Pillazo/VRCHaptics/VRChat Udon/Every100ms.PNG

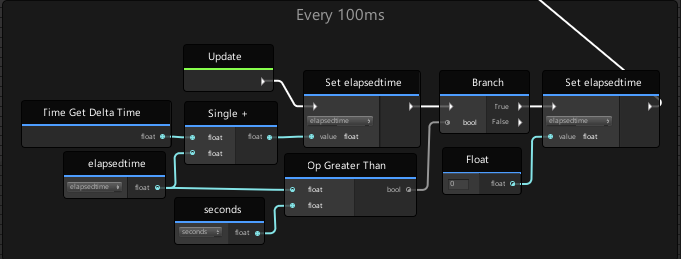
VRChat Udon/Every100ms.PNG
