Pillazo/VRCHaptics/VRChat Udon/For Each Other Player.PNG

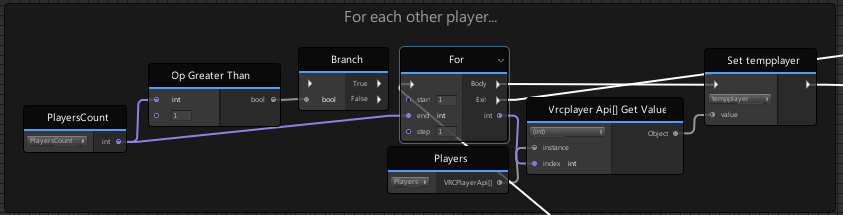
VRChat Udon/For Each Other Player.PNG
