Pillazo/VRCHaptics/VRChat Udon/Player Bones.PNG

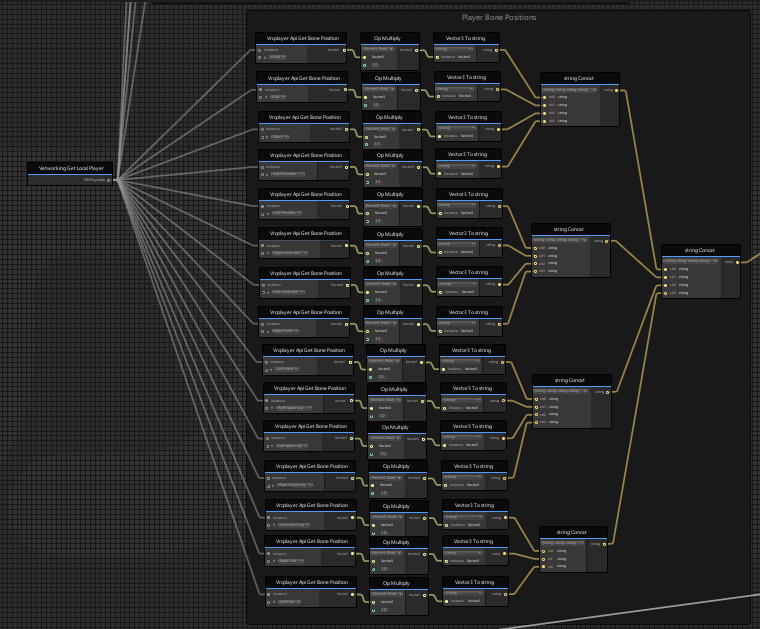
VRChat Udon/Player Bones.PNG
