Pillazo/VRCHaptics/VRChat Udon/Player Joined.PNG

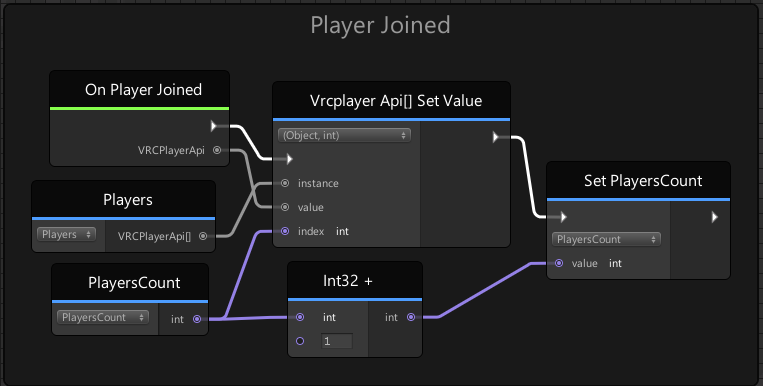
VRChat Udon/Player Joined.PNG
