Pillazo/VRCHaptics/VRChat Udon/Players Init.PNG

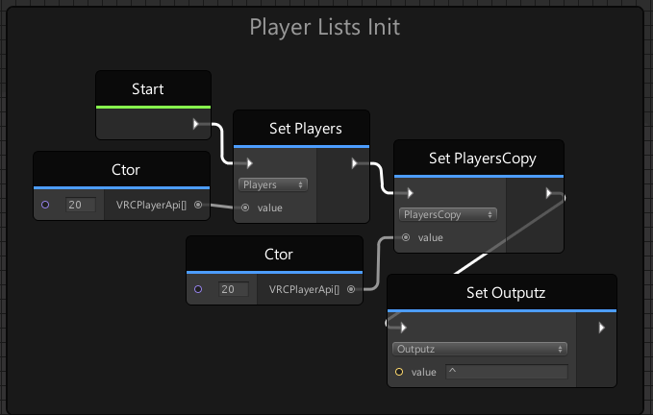
VRChat Udon/Players Init.PNG
