Pillazo/VRCHaptics/VRChat Udon/Send Packet.PNG

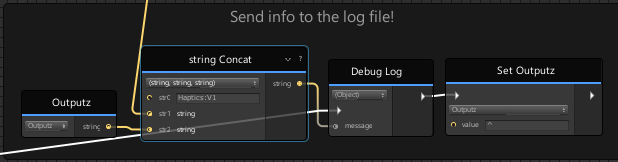
VRChat Udon/Send Packet.PNG
