Pillazo/VRCHaptics/VRChat Udon/Variables.PNG

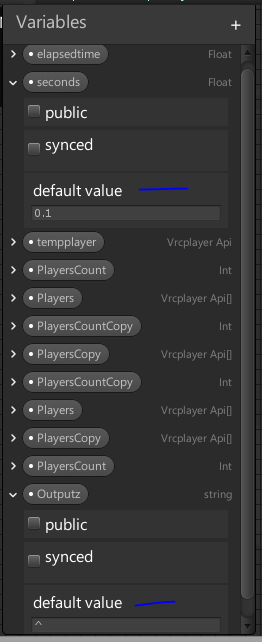
VRChat Udon/Variables.PNG
