Pillazo/VRCHaptics/VRChat Udon/VRCHaptics object.PNG

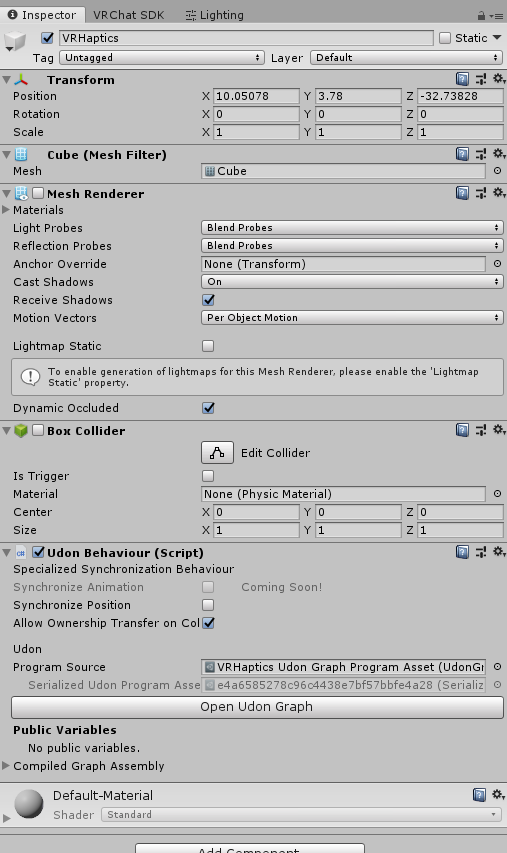
VRChat Udon/VRCHaptics object.PNG
