Pillazo/VRCHaptics/VRCHaptics 3D files/Ring.stl

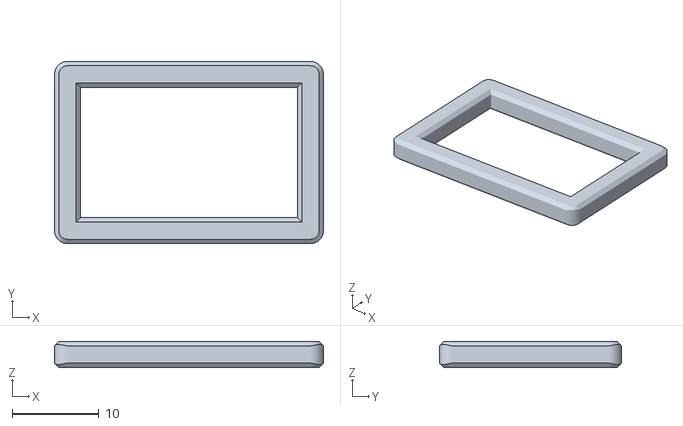
[picture p29: CAD file, 2020-08-08]
VRCHaptics 3D files/Ring.stl
31.0 x 21.0 x 3.00
