Pillazo/VRCHaptics/VRCHaptics 3D files/Main Body (1).3mf

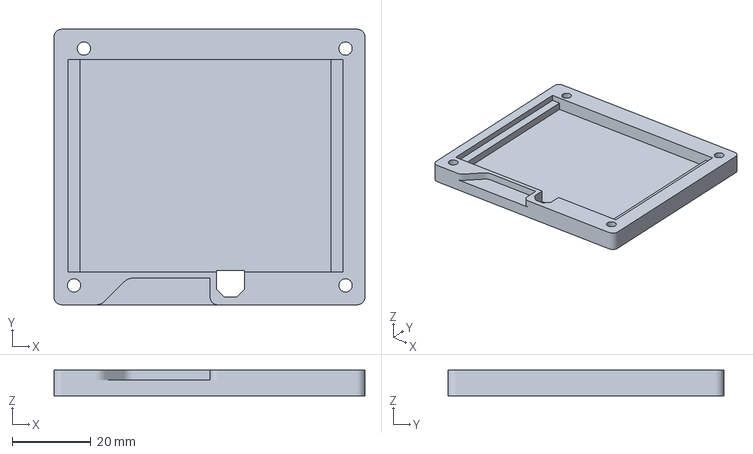
[picture p30: CAD file, 2020-08-09, an earlier design]
VRCHaptics 3D files/Main Body (1).3mf
79.2 x 70.2 x 6.50 mm
