Pillazo/VRCHaptics/VRChat Udon/Construct Packet.PNG

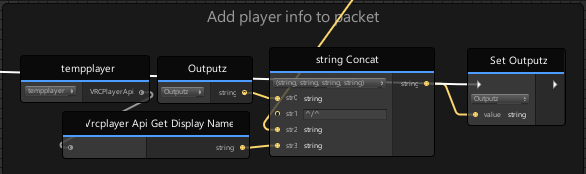
VRChat Udon/Construct Packet.PNG
